szepetamas/M3DMicroscope/Images/BracketHolder.jpg

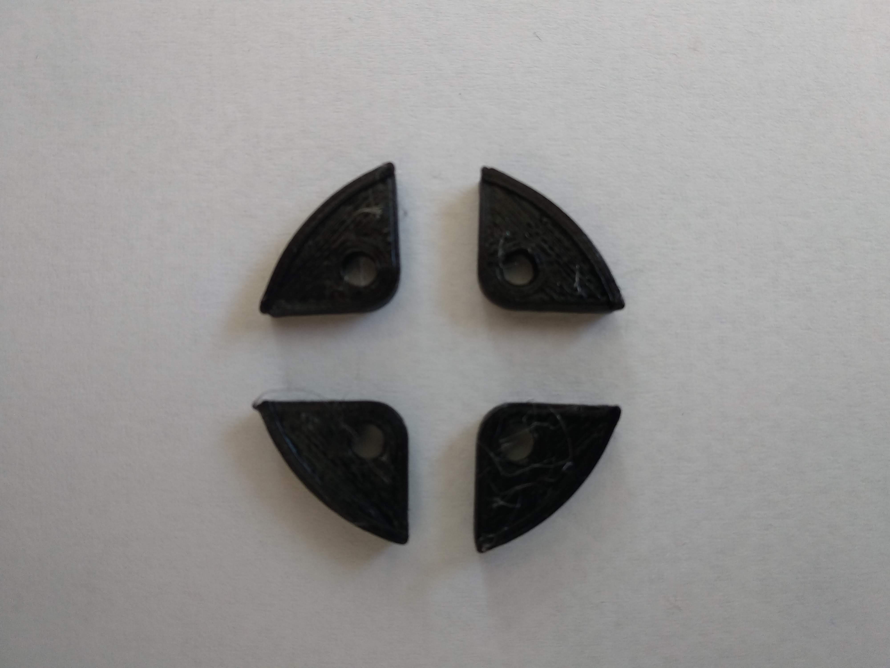
Images/BracketHolder.jpg
