szepetamas/M3DMicroscope/Images/M3Dexpert.png

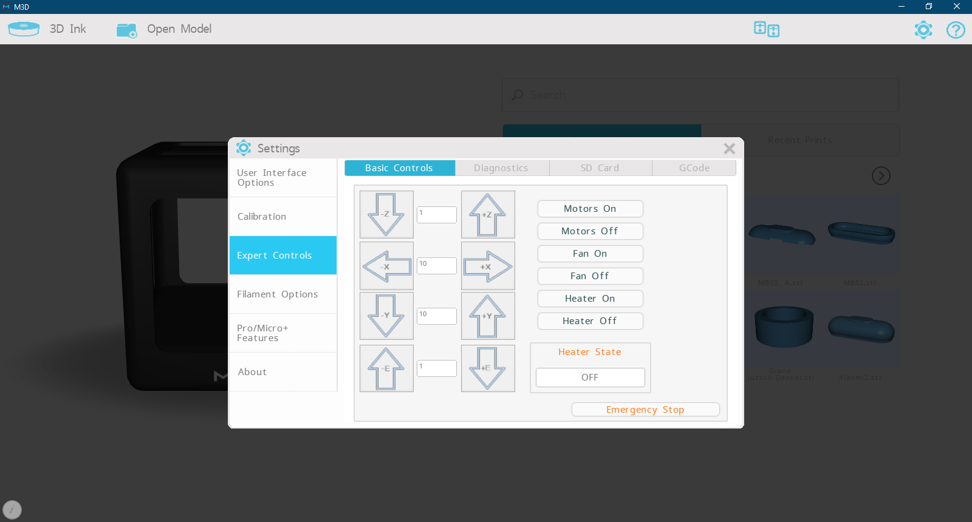
Images/M3Dexpert.png
