szepetamas/M3DMicroscope/Images/MicroscopeBackView.jpg

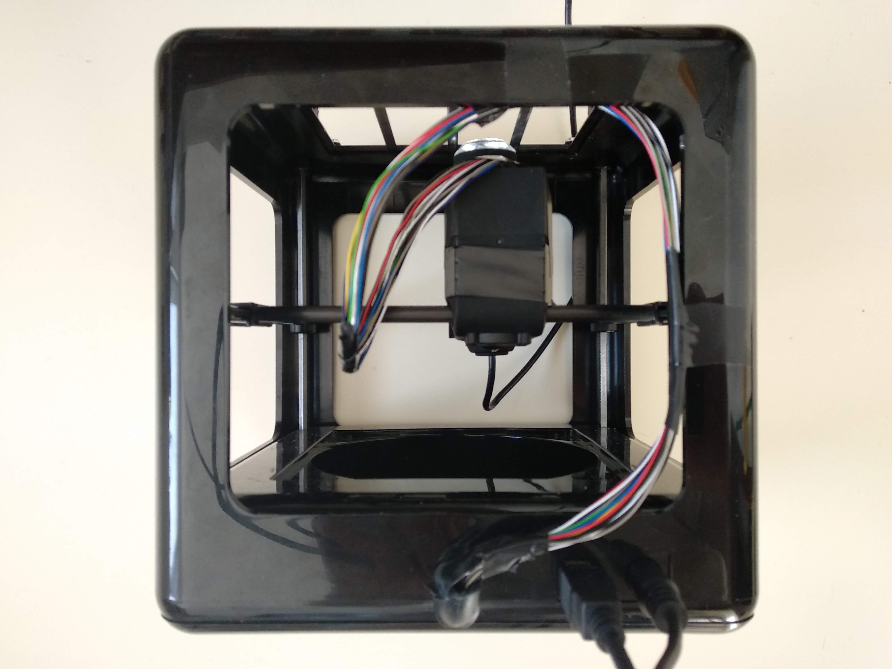
Images/MicroscopeBackView.jpg
