szepetamas/M3DMicroscope/Images/MicroscopeSideView.jpg

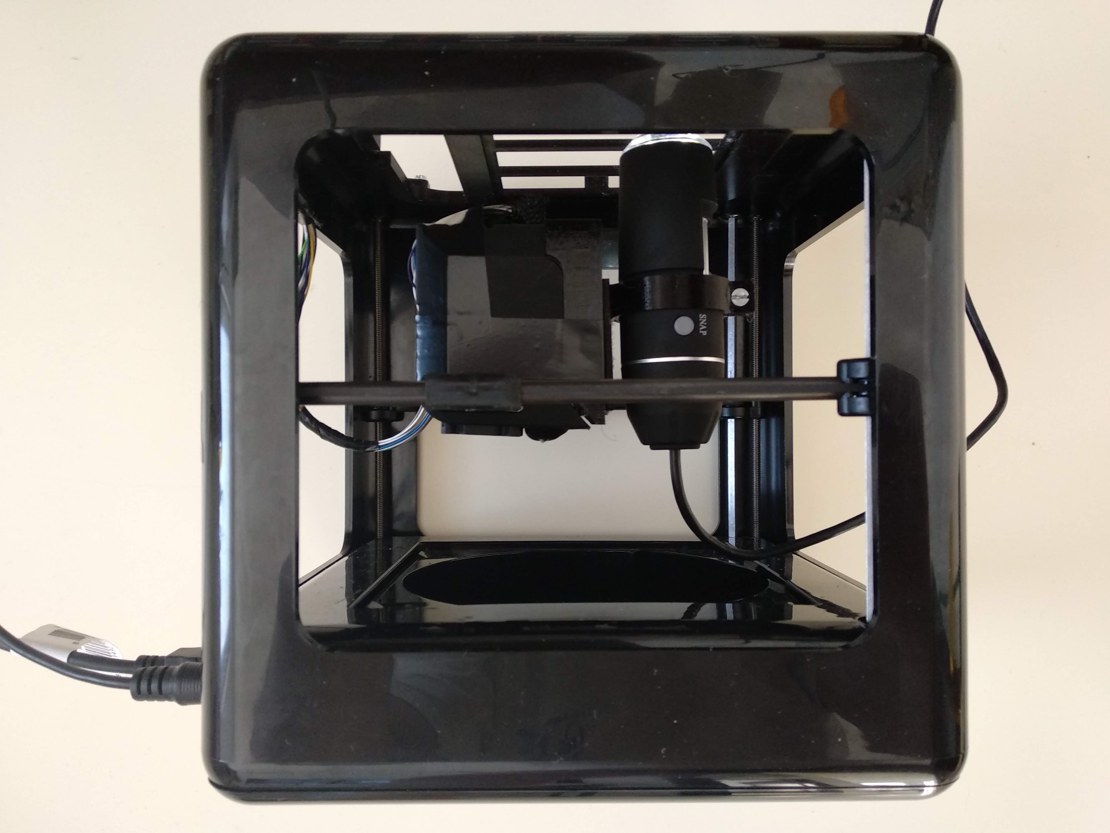
Images/MicroscopeSideView.jpg
