szepetamas/M3DMicroscope/Images/MicroscopeTopView.jpg

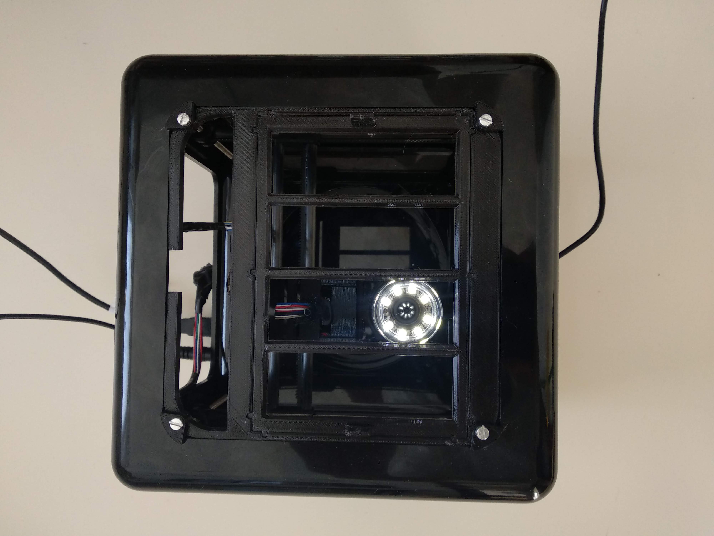
Images/MicroscopeTopView.jpg
