szepetamas/M3DMicroscope/Images/SliderBracket.jpg

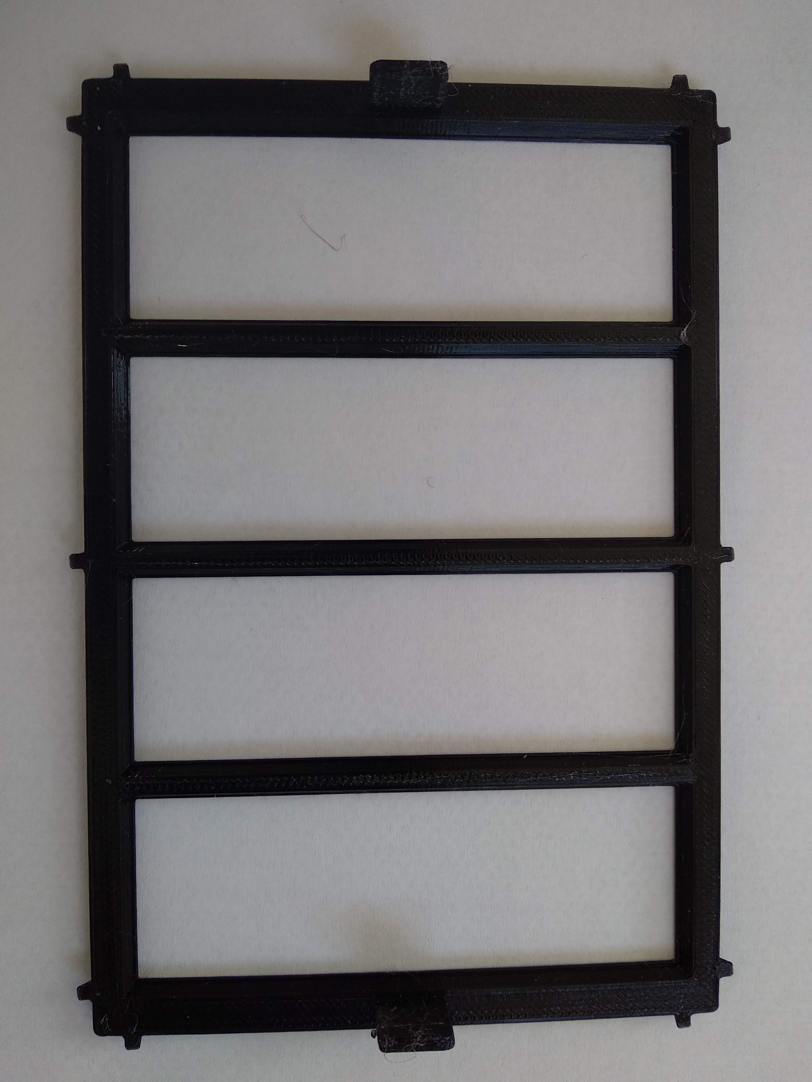
Images/SliderBracket.jpg
