szepetamas/M3DMicroscope/Images/PartsInSlic3r.png

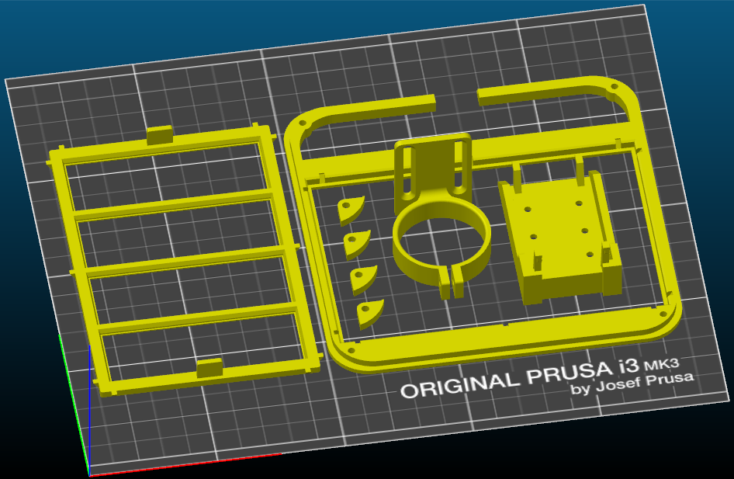
Images/PartsInSlic3r.png
