szepetamas/M3DMicroscope/Images/MicroscopeHeadAssembly2.jpg

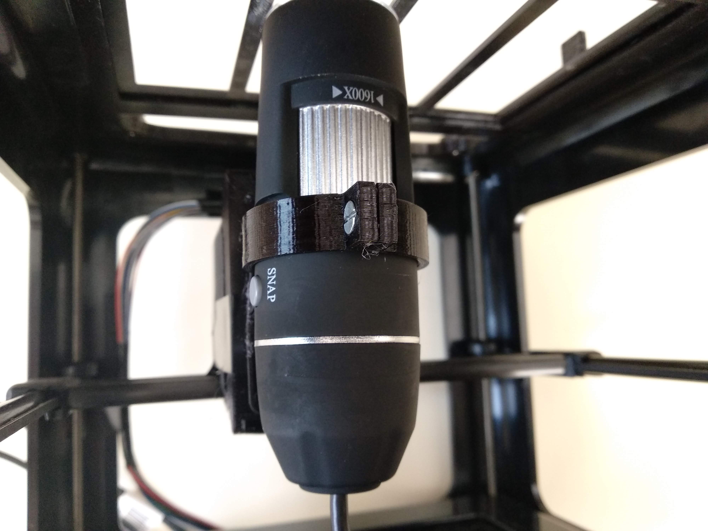
Images/MicroscopeHeadAssembly2.jpg
