szepetamas/M3DMicroscope/Images/MicroscopeHeadAssembly.jpg

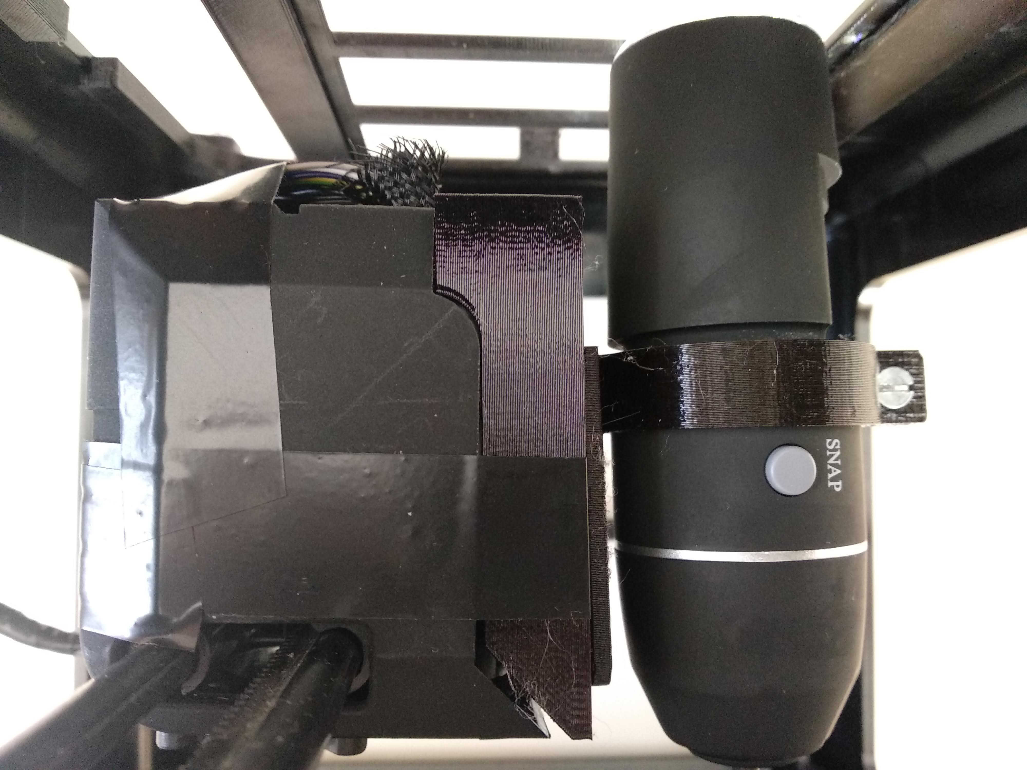
Images/MicroscopeHeadAssembly.jpg
